OpticalMoe/Bicycle_Light/0.Docs/IMG_20220910_073621.jpg

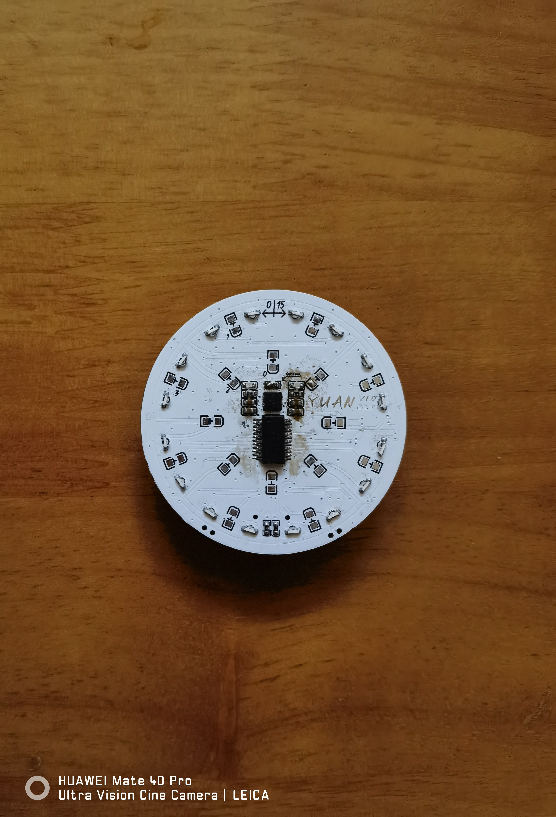
0.Docs/IMG_20220910_073621.jpg
