OpticalMoe/Bicycle_Light/2.Firmware/V0.1/Code/adc.h

/*!
 * @file        adc.h
 * @brief       adc
 * @copyright   Copyright (c) 2022 ChenYuanliang
 * @licence     CC-BY-NC-SA 3.0，知识共享许可协议-署名-非商业使用-相同方式共享。
 * @author      ChenYuanliang
 * @version     V1.0
 * @date        2022-09-01
 * @url         https://github.com/OpticalMoe
 */
 
#ifndef __ADC_H__
#define __ADC_H__

enum ADC_CHS
{
//    ADC_0 = 0x00,
//    ADC_1,
//    ADC_2,
//    ADC_3,
//    ADC_4,    
    ADC_5 = 0x05,
    ADC_6,
//    ADC_7,
//    ADC_8,
//    ADC_9,
//    ADC_10,
//    ADC_11,
//    ADC_12,
//    ADC_13,
//    ADC_14,
    ADC_1_19 = 0x0F
};

enum ENV
{
    DAYTIME ,
    EVENING ,
    NIGHT
};
extern enum ENV env;

enum BATTERY
{
    NO = 0 ,
    BAT
};
extern enum BATTERY battery;

void adc_init(void);
int adc_get_voltage(enum ADC_CHS adc_chs);
int adc_get_battery_electricity();


#endif
